vism2889/ECE_1895_junior_design_team_chi/pitt-traditions-arduino-ws/pitt-traditions/game-samples.h

/**************************************************************
 * AUTHOR(S):    Morgan Visnesky
 * DATE:         03/25/2022
 * FILENAME:     game-samples.h
 * ORGANIZATION: Junior Design Team CHI
 * TEAM MEMBERS: 
 *              Chris Guiher 
 *              Alex Shuster
 *              Morgan Visnesky
 *              David Cramer
 *
 * DESCRIPTION: 
 *     Holds game sample constants
 **************************************************************/

// IMPORTS
#include "PCM.h" // Library for MP3 playback

const unsigned char hailToPittSample[]    PROGMEM = {129, 126, 129, 127, 127, 129, 125, 129, 126, 128, 128, 126, 130, 125, 129, 128, 127, 130, 125, 130, 126, 128, 128, 125, 131, 124, 130, 128, 126, 130, 124, 131, 125, 128, 129, 125, 131, 124, 130, 127, 126, 130, 123, 131, 125, 128, 128, 124, 131, 123, 131, 127, 127, 130, 123, 132, 124, 129, 129, 124, 133, 123, 130, 126, 126, 131, 123, 132, 125, 129, 128, 124, 131, 123, 132, 125, 128, 131, 122, 133, 123, 129, 129, 123, 133, 121, 131, 126, 126, 132, 123, 134, 124, 129, 129, 122, 133, 122, 132, 126, 126, 131, 121, 135, 122, 129, 130, 120, 135, 121, 129, 128, 126, 134, 124, 136, 126, 132, 129, 121, 134, 118, 131, 126, 124, 134, 123, 133, 121, 129, 129, 124, 136, 120, 134, 131, 129, 132, 124, 132, 118, 131, 124, 128, 140, 115, 136, 119, 127, 134, 114, 144, 118, 130, 134, 120, 142, 123, 136, 120, 125, 133, 110, 138, 123, 128, 126, 129, 137, 126, 165, 107, 126, 133, 65, 144, 129, 136, 167, 139, 138, 103, 159, 114, 132, 214, 123, 195, 155, 108, 212, 152, 163, 118, 28, 44, 80, 199, 236, 208, 174, 103, 13, 0, 46, 88, 160, 224, 157, 96, 123, 160, 147, 234, 201, 56, 52, 21, 26, 110, 255, 245, 160, 224, 0, 0, 175, 0, 255, 255, 40, 204, 0, 0, 146, 117, 210, 255, 174, 133, 133, 0, 72, 181, 171, 255, 239, 86, 33, 44, 71, 177, 255, 137, 169, 54, 0, 157, 30, 163, 255, 125, 255, 94, 0, 179, 89, 130, 255, 138, 18, 156, 88, 0, 176, 135, 53, 255, 203, 106, 239, 84, 202, 255, 20, 196, 91, 0, 113, 151, 121, 255, 168, 3, 22, 0, 191, 210, 104, 255, 15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
87, 65, 144, 120, 103, 126, 118, 135, 119, 152, 183, 149, 88, 200, 132, 93, 163, 186, 182, 172, 213, 128, 190, 104, 100, 90, 106, 167, 94, 194, 124, 138, 118, 87, 138, 102, 72, 133, 192, 62, 104, 163, 85, 34, 123, 128, 77, 150, 184, 144, 75, 157, 132, 103, 124, 144, 163, 121, 130, 142, 109, 93, 155, 138, 120, 144, 147, 82, 84, 104, 83, 51, 110, 174};

const unsigned char panthersNoseSample[]  PROGMEM = {126, 127, 128, 127, 126, 126, 127, 129, 127, 126, 129, 126, 126, 129, 126, 129, 128, 125, 130, 127, 125, 128, 129, 129, 127, 127, 128, 130, 127, 129, 129, 125, 141, 140, 128, 140, 136, 131, 134, 130, 146, 161, 153, 138, 133, 135, 124, 117, 132, 151, 145, 125, 120, 132, 134, 119, 145, 177, 140, 123, 147, 132, 111, 121, 141, 137, 115, 123, 140, 128, 118, 129, 131, 123, 120, 121, 128, 127, 122, 125, 124, 122, 122, 120, 122, 123, 126, 123, 120, 127, 126, 121, 123, 124, 124, 131, 129, 120, 126, 127, 113, 110, 121, 123, 115, 119, 129, 117, 113, 125, 124, 119, 123, 128, 126, 118, 121, 127, 119, 113, 122, 131, 121, 115, 130, 129, 109, 115, 134, 122, 107, 131, 136, 112, 121, 132, 124, 118, 124, 133, 123, 118, 135, 128, 113, 122, 134, 123, 125, 140, 136, 126, 129, 130, 108, 103, 123, 130, 126, 136, 142, 129, 120, 127, 125, 116, 126, 126, 118, 123, 131, 131, 135, 128, 120, 124, 116, 116, 129, 131, 126, 127, 119, 116, 122, 117, 120, 126, 127, 128, 124, 116, 125, 123, 121, 139, 130, 116, 132, 132, 130, 128, 123, 132, 106, 124, 124, 102, 140, 137, 116, 132, 130, 138, 111, 97, 136, 110, 117, 144, 133, 142, 136, 114, 130, 111, 109, 149, 115, 117, 162, 97, 101, 165, 96, 108, 149, 119, 112, 115, 148, 128, 94, 162, 130, 93, 158, 124, 113, 160, 111, 126, 139, 112, 130, 115, 145, 136, 112, 146, 137, 119, 113, 101, 136, 105, 122, 147, 113, 141, 134, 121, 125, 125, 122, 147, 126, 139, 153, 111, 128, 138, 78, 133, 161, 101, 161, 130, 117, 136, 101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
 123, 129, 131, 126, 129, 123, 129, 128, 130, 129, 127, 126, 126, 131, 125, 126, 130, 128, 126, 123, 128, 129, 128, 128, 129, 132, 126, 128, 126, 130, 125, 125, 130, 126, 130, 125, 128, 130, 130, 126, 125, 132, 127, 128, 125, 128, 133, 123, 130, 127, 129, 126, 122, 129, 128, 129, 120, 132, 130, 127, 128, 123, 134, 126, 127, 129, 125, 126, 125, 129, 128, 132, 128, 126, 129, 125, 131, 125, 130, 131, 127, 127, 122, 126, 126, 130, 127, 131, 131, 122, 126, 130, 135, 124, 124, 132, 124, 122, 124, 133, 126, 120, 126, 129, 131, 125, 134, 130, 125, 129, 128, 127, 125, 131, 129, 125, 124, 123, 129, 126, 128, 132, 132, 129, 124, 126, 130, 129, 122, 122, 129, 129, 125, 124, 132, 134, 128, 126, 126, 129, 128, 125, 128, 133, 130, 122, 122, 127, 130, 127, 126, 131, 132, 128, 125, 127, 130, 128, 126, 127, 128, 128, 126, 125, 126, 129, 130, 129, 129, 130, 130, 125, 126, 128, 127, 126, 127, 127, 125, 127, 131, 130, 128, 129, 128, 125, 126, 127, 127, 126, 126, 128};

const unsigned char victoryLightsSample[] PROGMEM = {129, 129, 129, 129, 129, 129, 129, 129, 129, 128, 129, 128, 127, 127, 127, 127, 126, 126, 126, 125, 125, 125, 125, 125, 125, 126, 126, 127, 127, 127, 127, 128, 128, 129, 129, 130, 130, 131, 131, 131, 131, 131, 131, 131, 130, 130, 129, 128, 128, 127, 126, 125, 124, 124, 123, 123, 122, 122, 122, 122, 123, 123, 124, 125, 126, 127, 128, 129, 130, 131, 132, 133, 133, 134, 134, 134, 134, 134, 134, 133, 133, 131, 129, 128, 126, 124, 122, 120, 117, 115, 113, 113, 112, 111, 112, 113, 115, 118, 121, 125, 129, 131, 134, 137, 138, 140, 141, 142, 143, 144, 144, 144, 143, 142, 140, 138, 136, 133, 130, 127, 123, 119, 115, 112, 111, 108, 105, 104, 104, 105, 106, 109, 115, 119, 123, 127, 132, 135, 137, 138, 140, 140, 140, 141, 142, 142, 141, 140, 140, 138, 136, 134, 133, 132, 131, 130, 129, 129, 129, 128, 128, 127, 126, 126, 125, 124, 123, 123, 122, 121, 121, 120, 120, 119, 120, 121, 122, 123, 125, 126, 129, 131, 133, 134, 136, 138, 139, 139, 140, 140, 139, 138, 136, 135, 132, 128, 125, 120, 114, 110, 108, 104, 101, 99, 99, 100, 102, 106, 112, 118, 123, 129, 134, 138, 140, 143, 144, 146, 147, 148, 148, 149, 148, 147, 146, 144, 142, 139, 137, 136, 134, 131, 130, 129, 125, 123, 120, 117, 114, 112, 110, 106, 104, 103, 104, 104, 107, 112, 116, 120, 124, 128, 131, 132, 134, 136, 137, 138, 140, 142, 145, 144, 144, 145, 144, 142, 142, 141, 140, 140, 138, 137, 135, 133, 131, 126, 123, 118, 115, 113, 108, 105, 100, 99, 99, 98, 101, 107, 112, 117, 12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

const unsigned char hailToPittWinningJingle[] PROGMEM = {};
